stradiot/d-control-400-remote/include/pinout.h

#pragma once

// --- Pin Definitions ---
#define CC1101_MISO 0
#define CC1101_MOSI 3
#define CC1101_CS   10
#define CC1101_SCK  1
#define CC1101_GDO0 8

#define BUTTON_PIN 9 // BOOT button
#define LED_PIN 7    // LOLIN C3 Mini RGB LED
#define NUMPIXELS 1

#define LED_INDEX 0
